IOTA-Code/IOTA-GFT/IOTA-GFT/ublox.cpp

/*
	ublox.cpp 
	
	Routines for working with ublox GPS receivers.
  NOTES:
    *** uses millis() for timeout detection (Timer1 dependency)

*/

#include <Arduino.h>
#include "ublox.h"

//=================================================
//  ubxInit - initialize ublox GPS device
//
//  This version is for the UBX NEO-6 gps module
//    * uses millis() system call for timeout detection
//    * assumes NEO-6 boots to 9600 baud
//    * initializes NEO-6 to output the following SENTENCES on the serial port
//        $GPRMC
//        $GPGGA
//        $GPDTM
//        $PUBX,04
//
// return 0 on success
//    
//=================================================
int ubxInit()
{
  uint8_t enableRMC[] = {0x06, 0x01, 0x03, 0x00, 0xF0, 0x04, 0x01};       // Set GPRMC rate on current target
  uint8_t enableGGA[] = {0x06, 0x01, 0x03, 0x00, 0xF0, 0x00, 0x01};       // Set GPGGA rate on current target
  uint8_t enableDTM[] = {0x06, 0x01, 0x03, 0x00, 0xF0, 0x0A, 0x01};       // Set GPDTM rate on current target
  uint8_t enableGSV[] = {0x06, 0x01, 0x03, 0x00, 0xF0, 0x03, 0x01};       // Set GPGSV rate on current target
  uint8_t enablePUBX04[] = {0x06, 0x01, 0x03, 0x00, 0xF1, 0x04, 0x01};    // Set PUBX,04 rate on current target

  uint8_t disableGNSS[] = {0x06, 0x3E, 0x24, 0x00, 0x00, 0x10, 0x10, 0x04,
                                 0x00,0x04,0xFF,0x00,0x01,0x00,0x00,0x00,
                                 0x01,0x01,0x03,0x00,0x00,0x00,0x00,0x00,
                                 0x05,0x00,0x03,0x00,0x00,0x00,0x00,0x00,
                                 0x06,0x08,0xFF,0x00,0x00,0x00,0x00,0x00};    // disable SBAS, QZSS, GLONASS if present


  uint8_t configTimepulse[] = {0x06, 0x07, 0x14, 0x00,        //   configure timepulse
                          0x40, 0x42, 0x0F, 0x00,             // time interval = 1,000,000 us
                          0xA0, 0x86, 0x01, 0x00,             // pulse length = 100,000 us = 100ms
                          0x01,                               // positive pulse
                          0x00,                               // align to UTC
                          0x00,                               // time pulse only when sync'd to valid GPS
                          0x00,                               // reserved
                          0x00, 0x00,                         // Antenna cable delay
                          0x00, 0x00,                         // Receiver RF group delay
                          0x00, 0x00, 0x00, 0x00              // user time function delay
                          };
                                                   
  uint8_t configTP5[] = {0x06, 0x31, 0x20, 0x00,              //   configure timepulse via TP5 command  *** needs testing 
                          0x00,                               // timepulse
                          0x00, 0x00, 0x00,                   // reserved
                          0x32, 0x00,                         // antenna delay (ns)
                          0x00, 0x00,                         // RF group delay (ns)
                                                                // pps freq section
                          0x00, 0x00, 0x00, 0x00,             // freq when not locked => OFF
                          0x01, 0x00, 0x00, 0x00,             // freq when locked = 1hz
                                                                // pulse duration section
                          0x00, 0x00, 0x00, 0x00,             // when NOT locked => OFF
                          0xA0, 0x86, 0x01, 0x00,             // when LOCKED pulse length = 100,000 us = 100ms
                          0x00, 0x00, 0x00, 0x00,             // timepuse delay
                          0xFF, 0x00, 0x00, 0x00              // 11111111 = 0x7F 
                                                              // bit 7: gridUTCGPS = 1 = GPS
                                                              // bit 6: polarity = 1 = rising edge
                                                              // bit 5: alignToTOW = 1 = true
                                                              // bit 4: isLength = 1 = true
                                                              // bit 3: isFreq = 1 = true
                                                              // bit 2: lockedOtherSet = 1 = true
                                                              // bit 1: lockedGPSfreq = 1 = true
                                                              // bit 0: active = 1 = true
                          };
  uint8_t pollTP5[] = {0x06, 0x31, 0x00, 0x00};    // poll settings for timepulse 0
                          
                          
  // 9600 NMEA is the default rate for the GPS
  //
  gpsSerial.begin(9600);
  
  //********************************
  //  TURN OFF everything to keep the serial port quiet
  //
  gpsSerial.println("$PUBX,40,RMC,0,0,0,0,0,0*46");   // RMC OFF
  gpsSerial.flush(); // wait for it...

  gpsSerial.println("$PUBX,40,GGA,0,0,0,0,0,0*5A");   // GGA OFF
  gpsSerial.flush(); // wait for it...

  gpsSerial.println("$PUBX,40,DTM,0,0,0,0,0,0*46");   // DTM OFF
  gpsSerial.flush(); // wait for it...

  gpsSerial.println("$PUBX,40,VTG,0,0,0,0,0,0*5E");   // VTG OFF
  gpsSerial.flush(); // wait for it...

  gpsSerial.println("$PUBX,40,GSA,0,0,0,0,0,0*4E");   // GSA OFF
  gpsSerial.flush(); // wait for it...

  gpsSerial.println("$PUBX,40,GSV,0,0,0,0,0,0*59");   // GSV OFF
  gpsSerial.flush(); // wait for it...

  gpsSerial.println("$PUBX,40,GLL,0,0,0,0,0,0*5C");   // GLL OFF
  gpsSerial.flush(); // wait for it...

  // wait 100ms and empty any pending incoming data
  //
  delay(100);
  while (gpsSerial.available())
    gpsSerial.read();

  //
  // *** need to switch to using CFG-TP5 message for compatibility with later firmware.
  //     In the meantime, leaving the default timepulse configuration is fine
  //
#if (INIT_TP == 1)
  // configure timepulse
  //
  ubxSend(configTP5,sizeof(configTP5)/sizeof(uint8_t));
  if (!ubxGetAck(configTP5))
  {
    return gps_E_CFGTP;
  }
#endif


  //*********************************
  //  TURN ON sentences that we want
  //    GPRMC
  //    GPGGA
  //    GPDTM
  //    PUBX,04
  //
  ubxSend(enableRMC,sizeof(enableRMC)/sizeof(uint8_t));
  if (!ubxGetAck(enableRMC))
  {
    return gps_E_RMC;
  }

  
  ubxSend(enableGGA,sizeof(enableGGA)/sizeof(uint8_t));
  if (!ubxGetAck(enableGGA))
  {
    return gps_E_GGA;
  }

  ubxSend(enableDTM,sizeof(enableDTM)/sizeof(uint8_t));
  if (!ubxGetAck(enableDTM))
  {
    return gps_E_DTM;
  }

  ubxSend(enablePUBX04,sizeof(enablePUBX04)/sizeof(uint8_t));
  if (!ubxGetAck(enablePUBX04))
  {
    return gps_E_PUBX04;
  }

  //************************************
  //  Disable SBASS, QZSS and GNSS if present
  //************************************
  ubxSend(disableGNSS,sizeof(disableGNSS)/sizeof(uint8_t));
  if (!ubxGetAck(disableGNSS))
  {
    return gps_E_GNSS;
  }


  return gps_OK;
  
} // end of ubxInit

//=================================================
//  ubxSend
//
//  Send a UBX command to the GPS
//    MSG = byte array containing the UBX command data
//    len = # of bytes in MSG
//=================================================
void ubxSend(uint8_t *MSG, uint32_t len) 
{

  uint32_t CK_A = 0, CK_B = 0;
  uint8_t sum1=0x00, sum2=0x00;
  uint8_t ubxPacket[len+4];


  // UBX prefixes
  //
  ubxPacket[0]=0xB5;
  ubxPacket[1]= 0x62;
  
  for(int i=0; i<len; i++) 
  {
    ubxPacket[i+2]=MSG[i];
  }

  // Calculate checksum
  //
  for(int i=0; i<len; i++)
  {
    CK_A = CK_A + MSG[i];
    CK_B = CK_B + CK_A;
  }
  sum1 = CK_A &0xff;//Mask the checksums to be one byte
  sum2= CK_B &0xff;

  // add the checksum to the end of the UBX packet
  //
  ubxPacket[len+2]=sum1;
  ubxPacket[len+3]=sum2;
 
  // send the UBX command
  //
  gpsSerial.write(ubxPacket,len+4);
  gpsSerial.flush();  // wait for it ...
  
}   // end of sendUBX

//=================================================
//    ubxGetAck - wait for ack after command
//
//=================================================
bool ubxGetAck(uint8_t *MSG)
{
  
  uint8_t b;
  uint8_t ackByteID;
  uint8_t ackPacket[10];
  uint8_t ackReceived[10];
  unsigned long startTime;
  unsigned long currentTime;
  unsigned long waitTime;
  uint32_t CK_A=0, CK_B=0;

  //*********************************
  // Construct the expected ACK packet    
  //
  ackPacket[0] = 0xB5;  // header
  ackPacket[1] = 0x62;  // header
  ackPacket[2] = 0x05;  // class
  ackPacket[3] = 0x01;  // id
  ackPacket[4] = 0x02;  // length
  ackPacket[5] = 0x00;
  ackPacket[6] = MSG[0];    // MGS class
  ackPacket[7] = MSG[1];    // MSG id
  ackPacket[8] = 0;     // CK_A
  ackPacket[9] = 0;     // CK_B

  // checksums
  //
  for (uint8_t i=2; i<8; i++) 
  {
    CK_A = CK_A + ackPacket[i];
    CK_B= CK_B + CK_A;
  }

  ackPacket[8]= CK_A &0xff;//Mask the checksums to be one byte
  ackPacket[9]= CK_B &0xff;

  //***********************************************
  // get the 10 byte ack packet (with timeout)
  //  wait for first header byte of ACK (0xB5) - should arrive within timeout period..
  //    
  //
  startTime = millis();
 
  
  for( int i = 0; i < 10;  )
  {

    // Timeout if no ACK in 500ms
    //
    //
    currentTime = millis();
    if (currentTime >= startTime)
    {
      waitTime = currentTime - startTime;
    }
    else
    {
      // rollover
      waitTime = 0 - (startTime - currentTime);
    }
    if (waitTime > 500)
    {
      return false;   // timeout
    }

    // got a byte?
    //   if starting header, save it and continue
    //
    if (gpsSerial.available()) 
    {
      b = gpsSerial.read();
      ackReceived[i] = b;
      if (i != 0)
      {
        i++;    // next byte
      }
      else
      {
        // i == 0
        // we are looking for the first byte of the header
        //  move forward IFF the data bye matches the first header byte value
        if (b == 0xB5)
        {
          // ok, we have the starting header byte and can move forward
          //
          i++;
        }
      } // end of i== 0 check

    } // end of check for data available
    
  } // end of for loop to get the bytes

  //****************************
  //  check the packet
  //
  for( int i = 0; i < 10; i++ )
  {
    if (ackReceived[i] != ackPacket[i])
    {
      return(false);
    }
  }  // end of checking the received packet

  //*********************
  //  all OK
  //
  return( true );
    
} // end of ubxAck
